christianstaresina/laser-timer-system-v1/firmware/receiver/laser_timer_v2_rx/src/menu_rx.h

/**
 * menu_rx.h
 * Laser Timer Firmware v2 — non-blocking table-driven menu system
 */

#ifndef MENU_RX_H
#define MENU_RX_H

#include <Arduino.h>

enum MenuScreen : uint8_t {
  MS_Idle = 0,
  MS_Splash,
  MS_Main,
  MS_Distance,
  MS_Custom,
  MS_Radio,
  MS_Buzzer,
  MS_RePairing
};

void menuInit();
void menuRequestOpen();
bool menuIsActive();
void menuRefresh();
void menuTick();

#endif
